zhuyuezx/CSC494_holoprojector/Code/imgs/target_raw.bmp

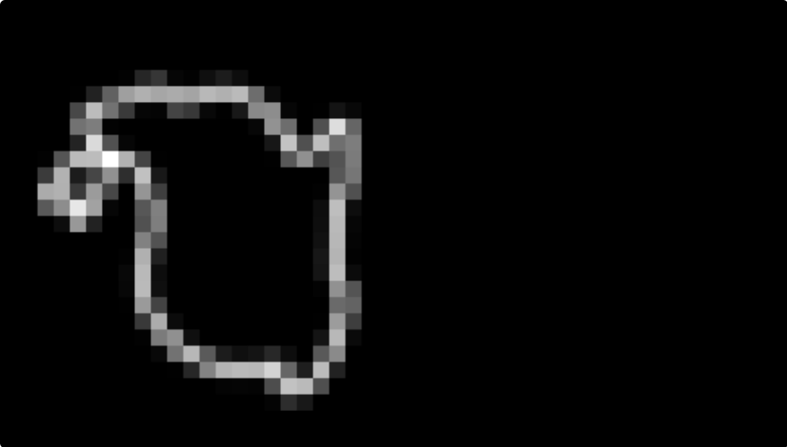
Code/imgs/target_raw.bmp
