zhuyuezx/CSC494_holoprojector/Code/saved_frames/image0.png

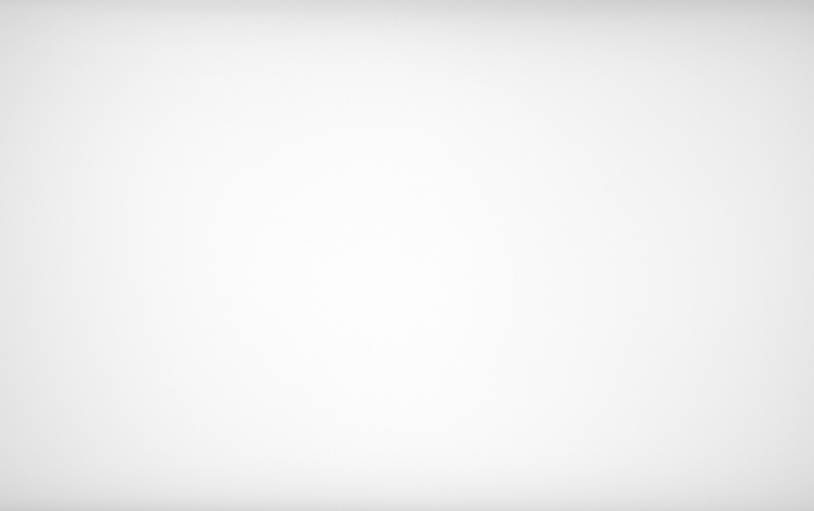
Code/saved_frames/image0.png
