zhuyuezx/CSC494_holoprojector/Code/saved_frames/image3.bmp

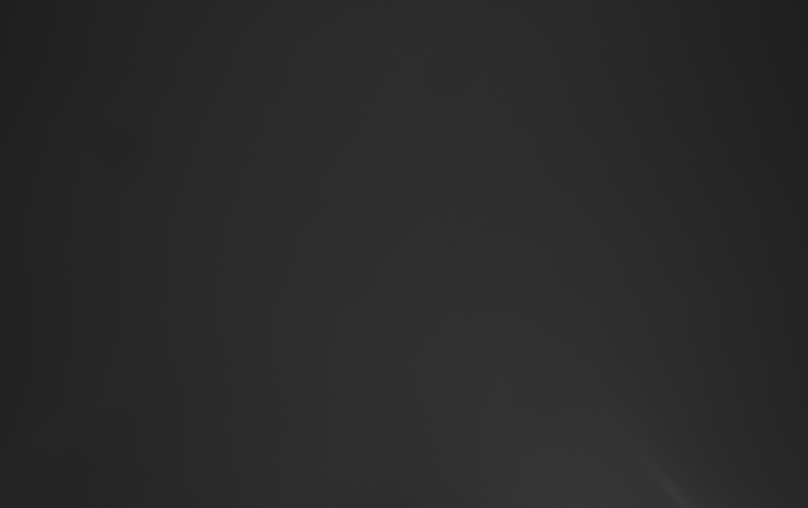
Code/saved_frames/image3.bmp
