zhuyuezx/CSC494_holoprojector/DMD_inputs/678_Block.bmp

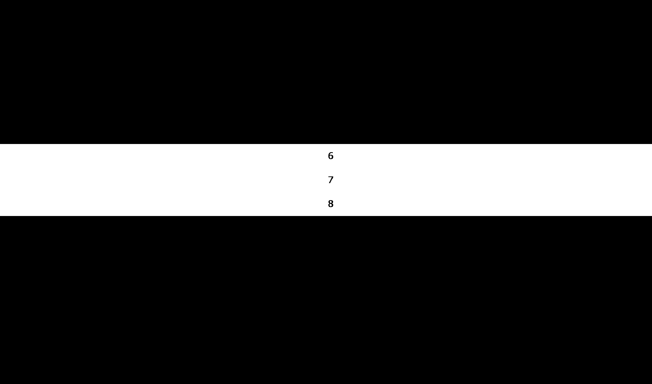
DMD_inputs/678_Block.bmp
