zhuyuezx/CSC494_holoprojector/DMD_inputs/half_size/circle_2.bmp

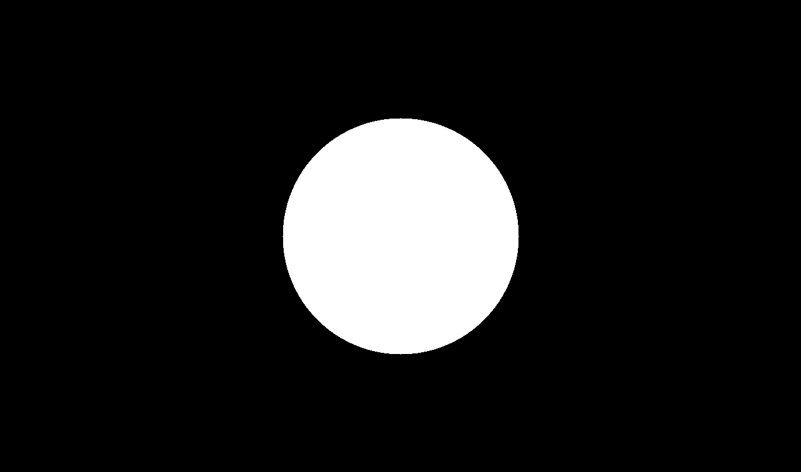
DMD_inputs/half_size/circle_2.bmp
