zhuyuezx/CSC494_holoprojector/DMD_inputs/half_size/circle_3.bmp

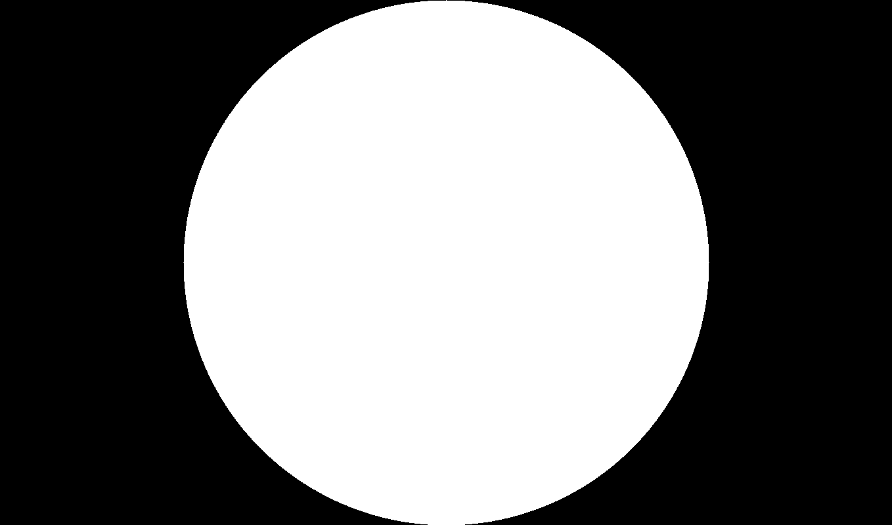
DMD_inputs/half_size/circle_3.bmp
