zhuyuezx/CSC494_holoprojector/laser_shots/100us/2h_100us_1.png

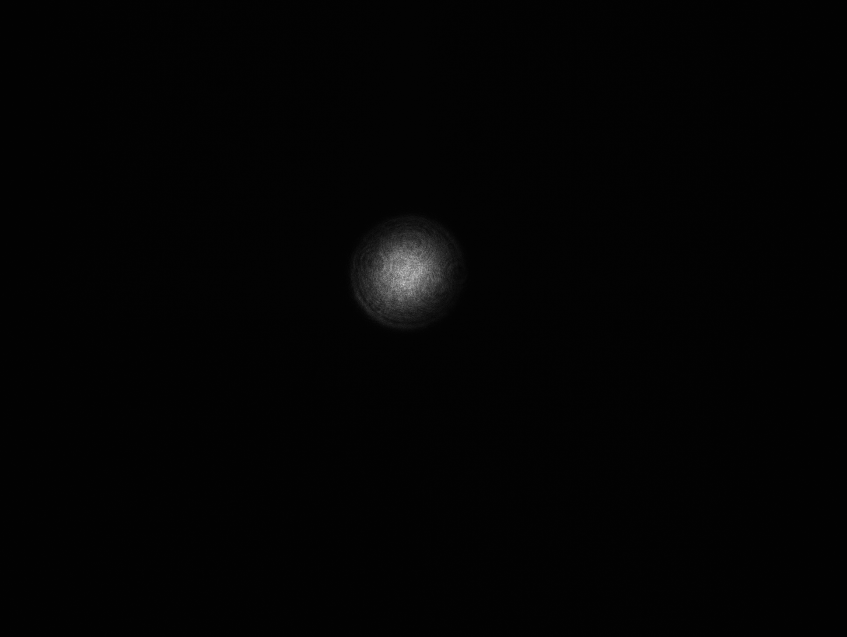
laser_shots/100us/2h_100us_1.png
