zhuyuezx/CSC494_holoprojector/laser_shots/100us/4h_100us.png

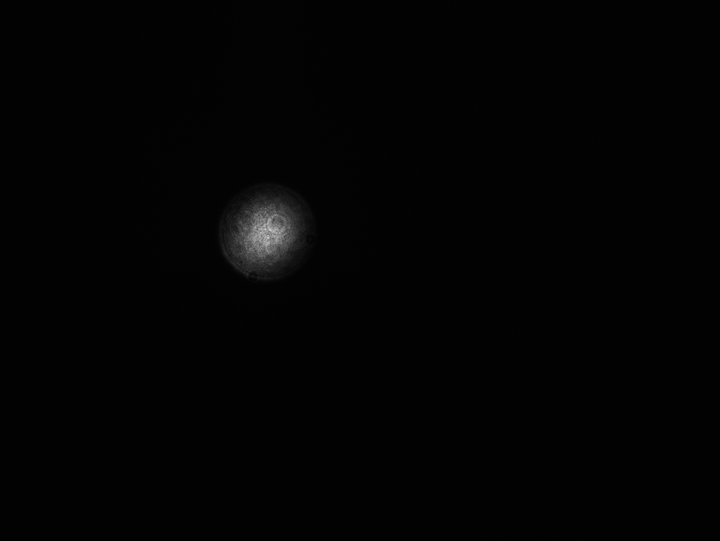
laser_shots/100us/4h_100us.png
