zhuyuezx/CSC494_holoprojector/laser_shots/2000us/6h_2000us.png

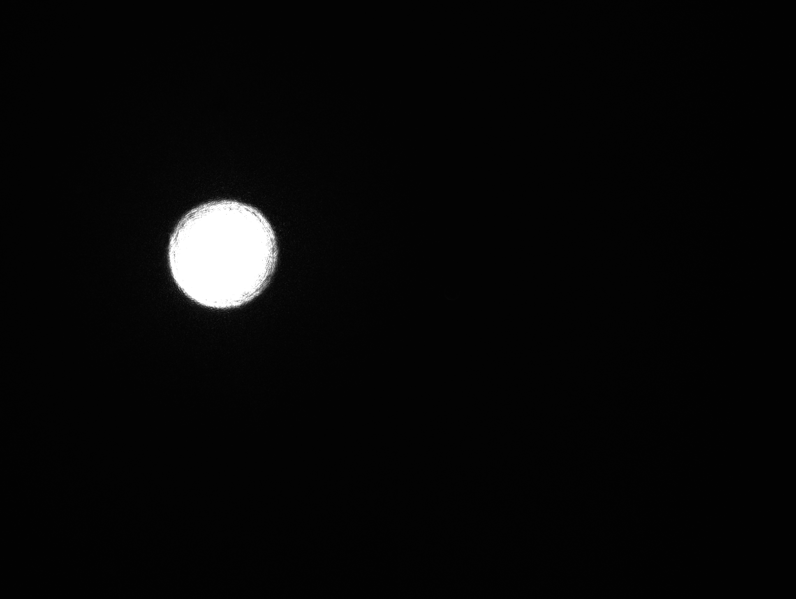
laser_shots/2000us/6h_2000us.png
