zhuyuezx/CSC494_holoprojector/laser_shots/2000us/12h_2000us.png

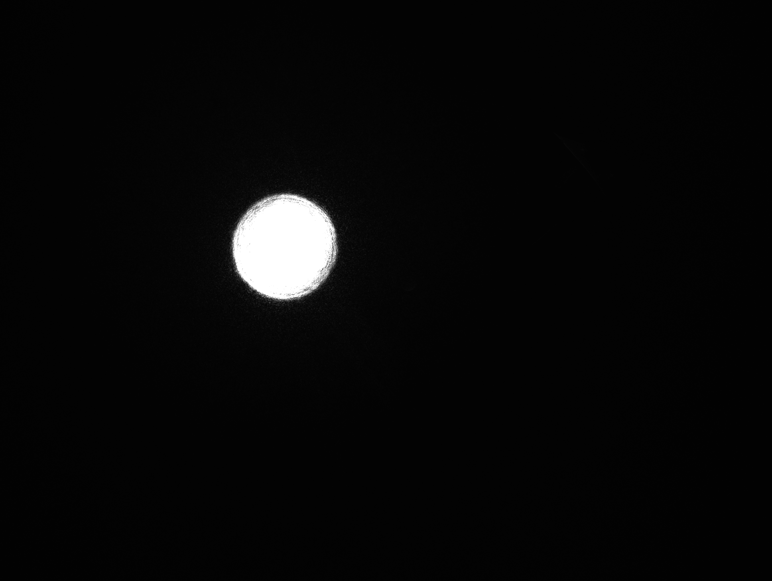
laser_shots/2000us/12h_2000us.png
