zhuyuezx/CSC494_holoprojector/laser_shots/circles/4_px.png

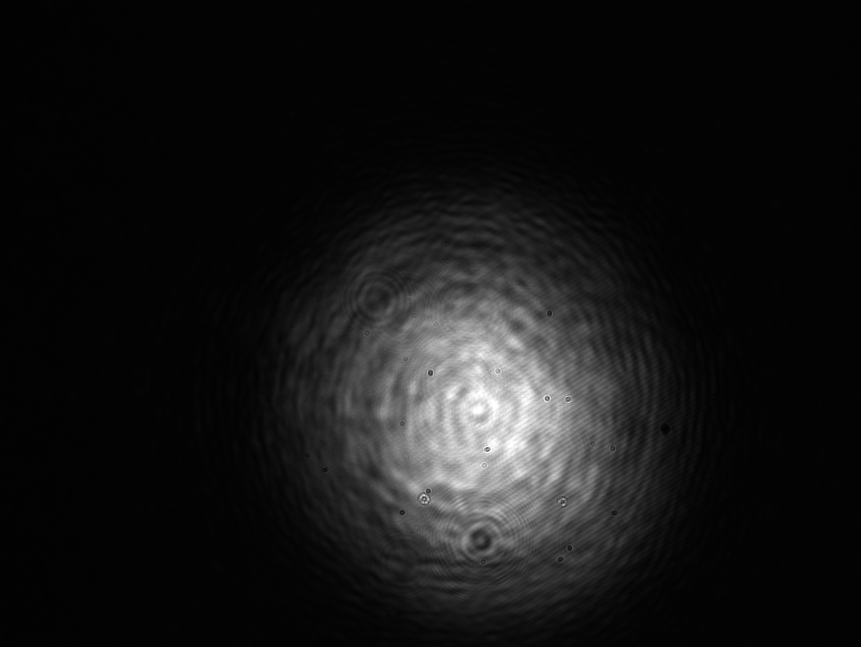
laser_shots/circles/4_px.png
