zhuyuezx/CSC494_holoprojector/laser_shots/line_far_away/half_half.png

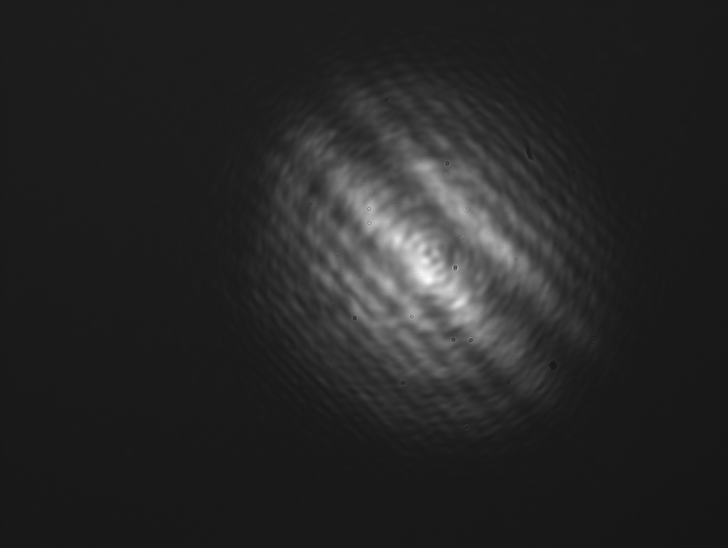
laser_shots/line_far_away/half_half.png
