zhuyuezx/CSC494_holoprojector/laser_shots/line_far_away/raw_2px.png

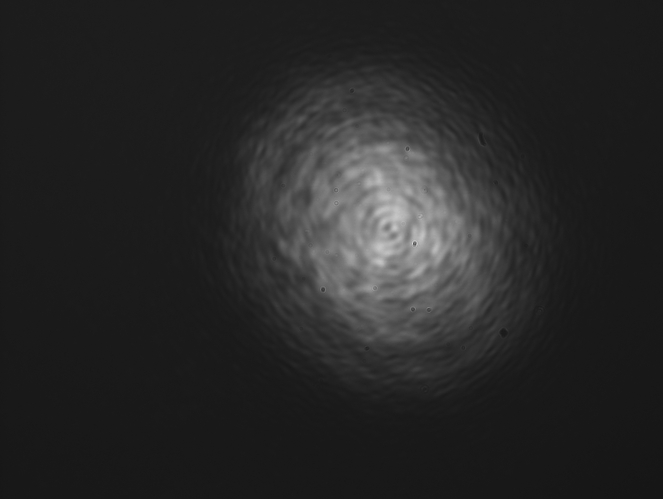
laser_shots/line_far_away/raw_2px.png
