zhuyuezx/CSC494_holoprojector/laser_shots/rings/2_px.png

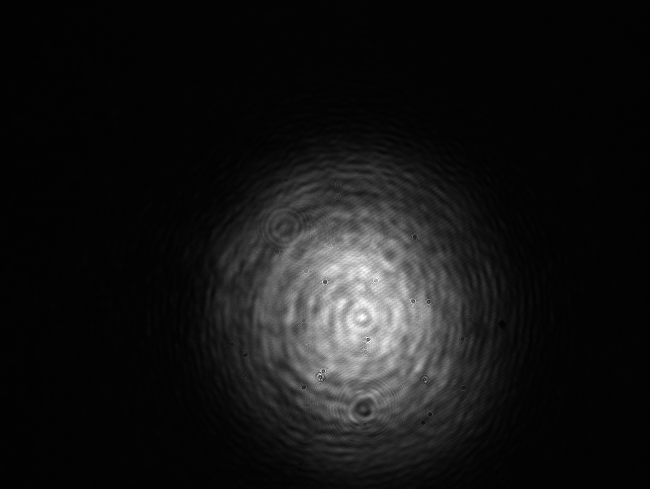
laser_shots/rings/2_px.png
