zhuyuezx/CSC494_holoprojector/laser_shots/rings/32_px.png

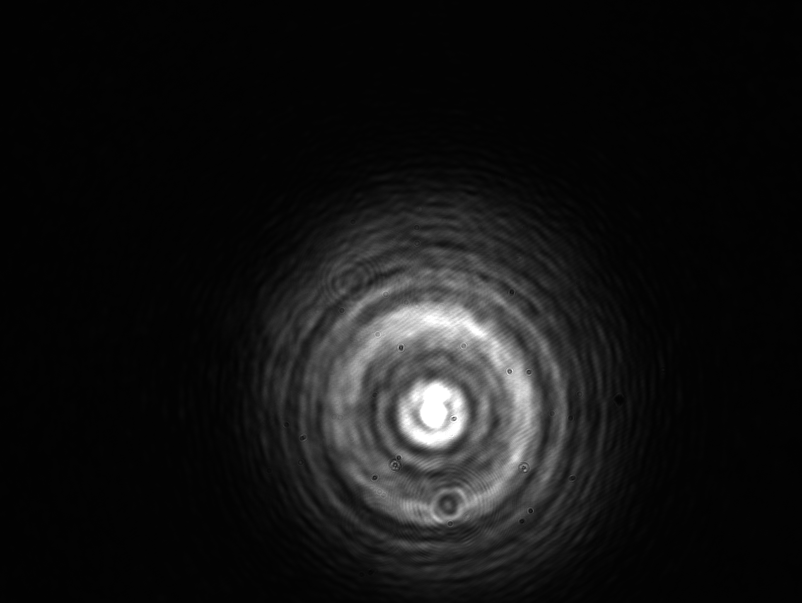
laser_shots/rings/32_px.png
