zhuyuezx/CSC494_holoprojector/laser_shots/tridents/1d_1.png

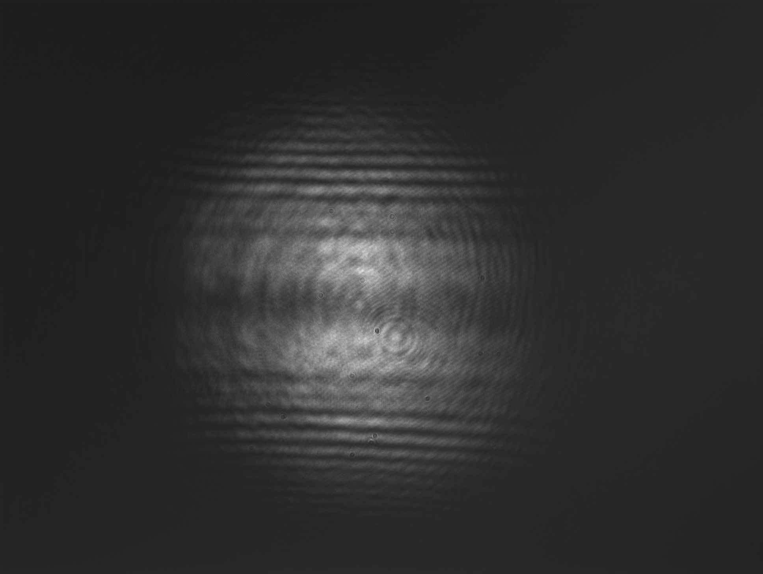
laser_shots/tridents/1d_1.png
