zhuyuezx/CSC494_holoprojector/laser_shots/tridents/2d_2.png

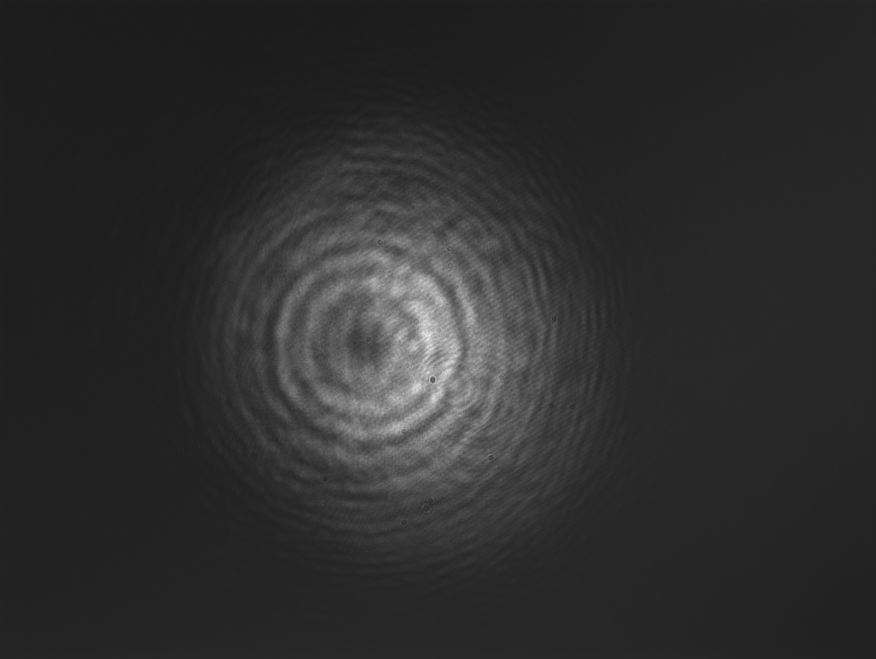
laser_shots/tridents/2d_2.png
