zhuyuezx/CSC494_holoprojector/Code/results/distributions_manual_midpoint.png

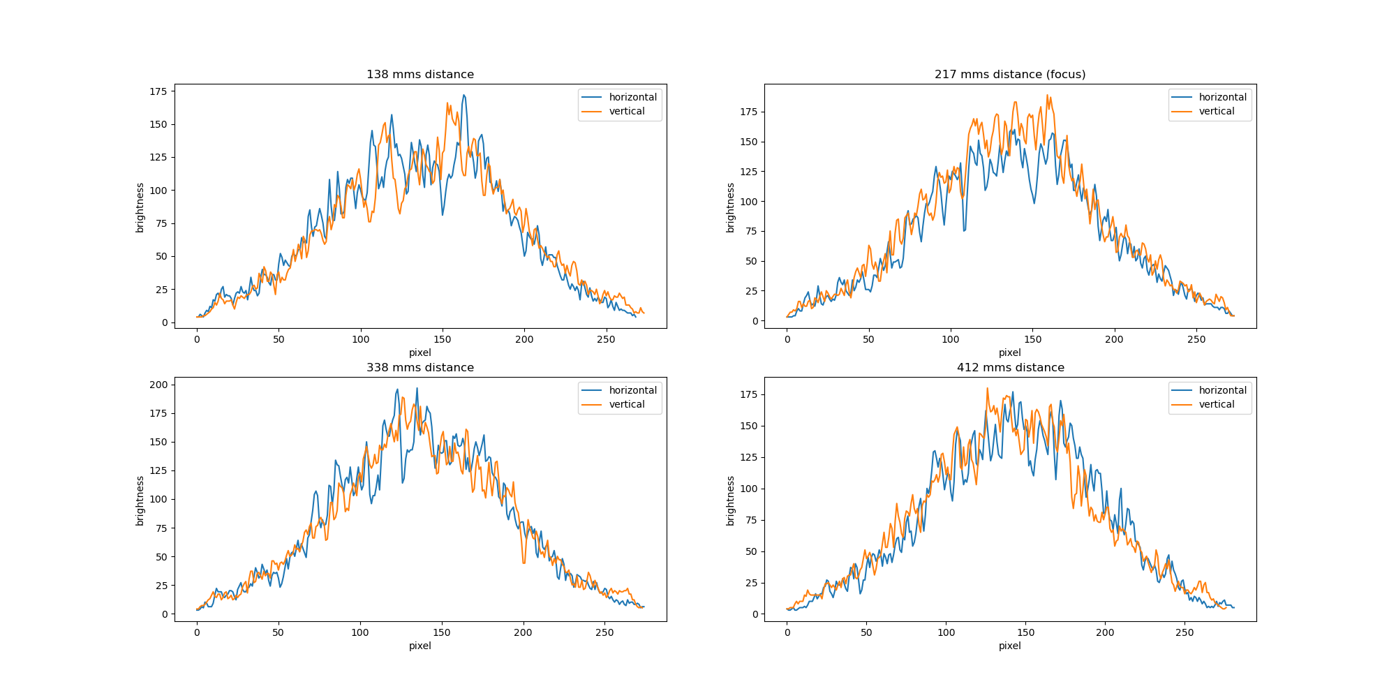
Code/results/distributions_manual_midpoint.png
