zhuyuezx/CSC494_holoprojector/Code/results/cmp_h.png

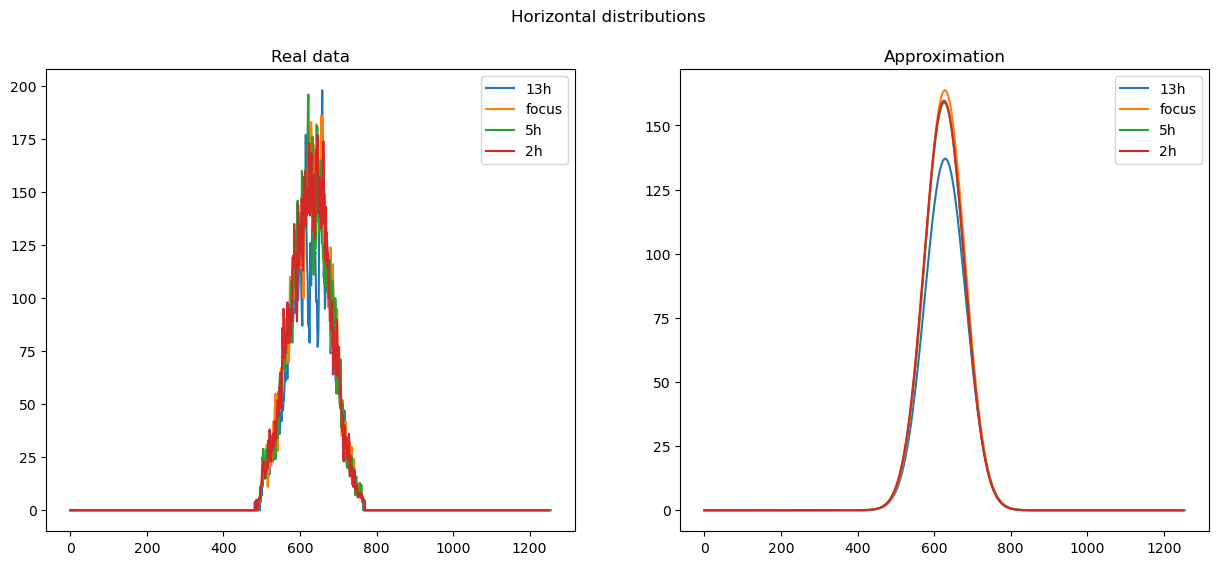
Code/results/cmp_h.png
