zhuyuezx/CSC494_holoprojector/Code/results/cropped_scale.png

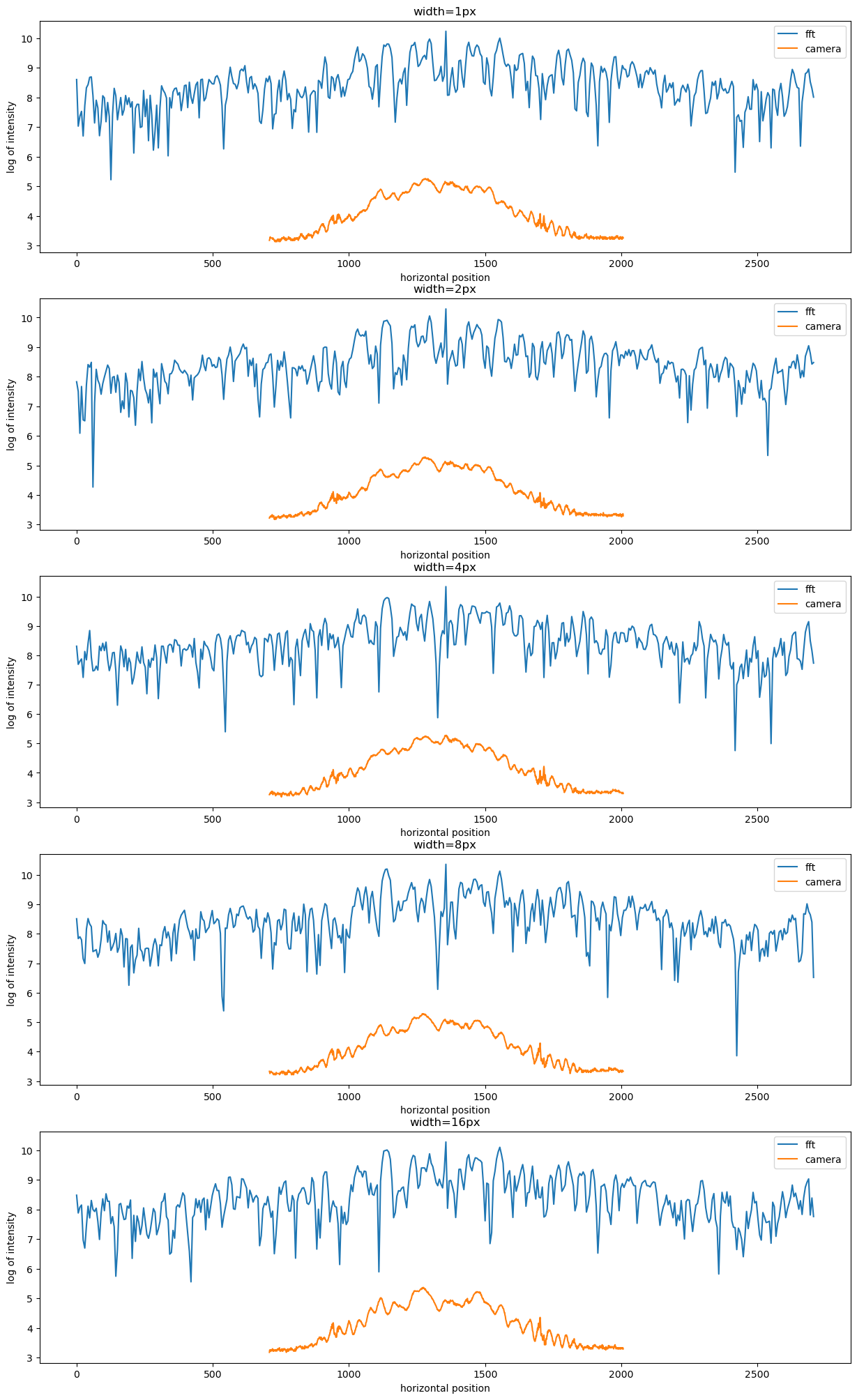
Code/results/cropped_scale.png
