zhuyuezx/CSC494_holoprojector/Code/results/distribution_plots.png

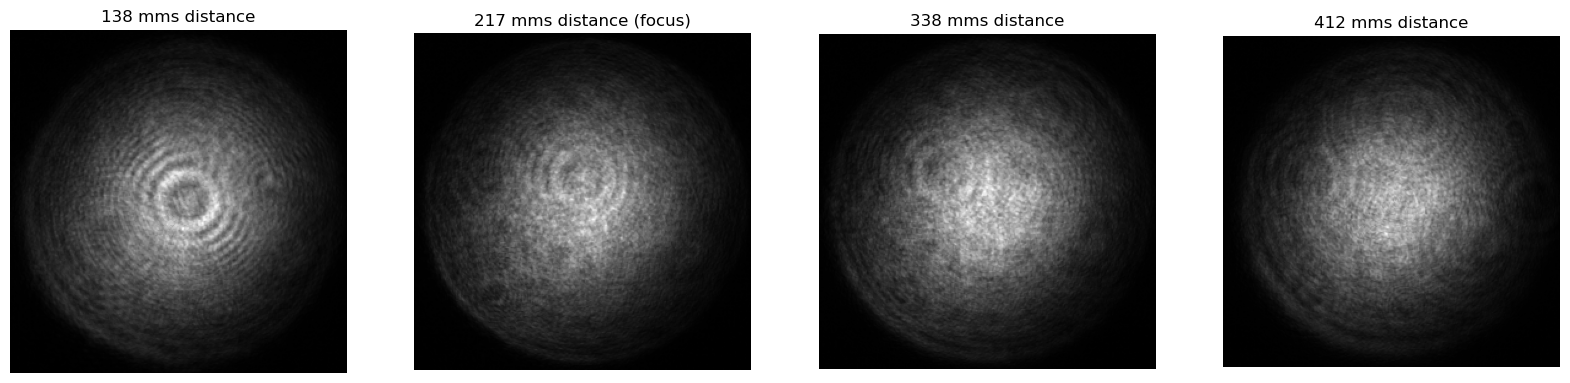
Code/results/distribution_plots.png
