zhuyuezx/CSC494_holoprojector/Code/results/orig_scale.png

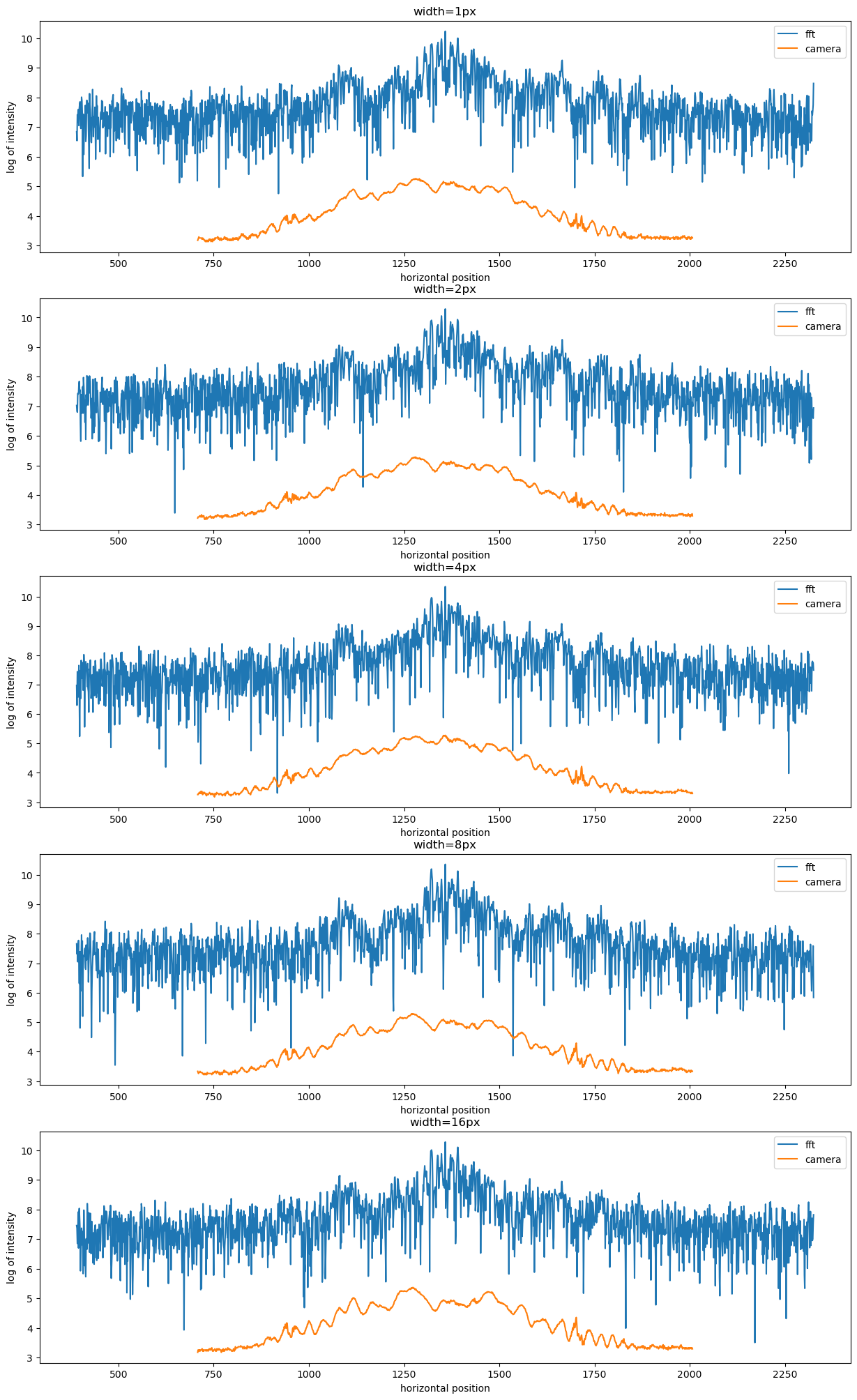
Code/results/orig_scale.png
