zhuyuezx/CSC494_holoprojector/Code/results/sigma_distribution.png

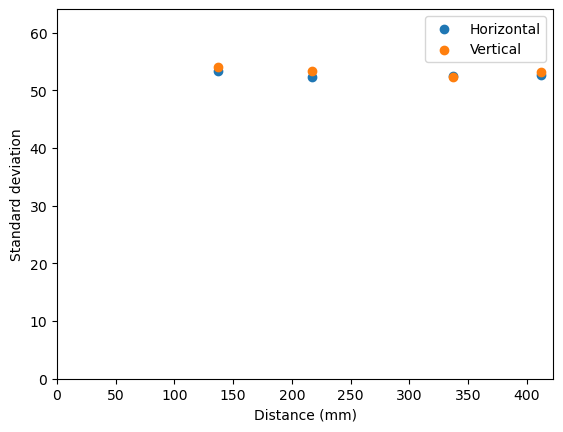
Code/results/sigma_distribution.png
