zhuyuezx/CSC494_holoprojector/Code/results/sigma_distribution_close.png

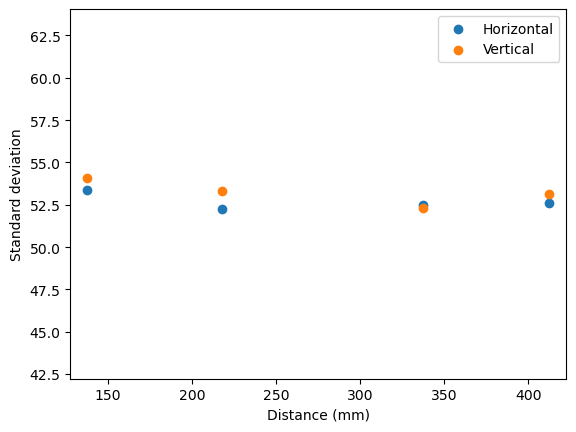
Code/results/sigma_distribution_close.png
